AmigusLabs/BarcoSolar-2019/STL/sec6.stl

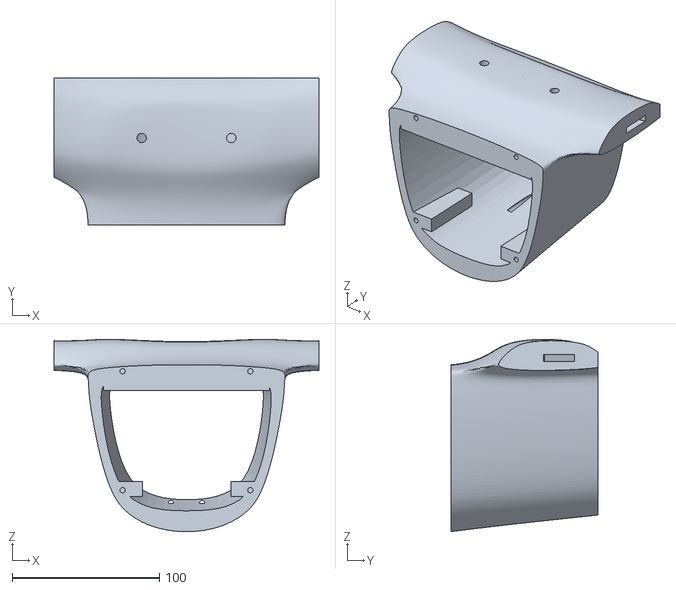
[picture p15: CAD file, 2019-10-26]
STL/sec6.stl
180.0 x 100.0 x 130.6
