AmigusLabs/BarcoSolar-2019/STL/soporte_servo.stl

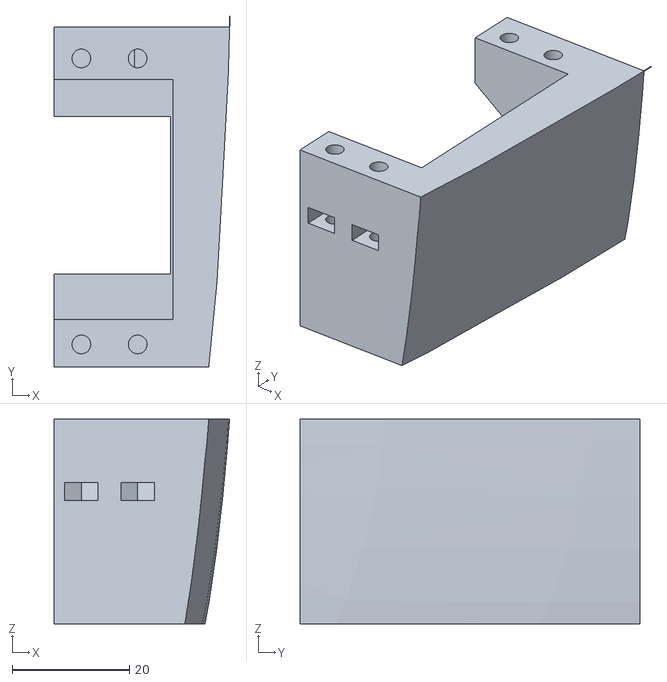
[picture p16: CAD file, 2019-10-26]
STL/soporte_servo.stl
30.0 x 59.9 x 35.0
