AmigusLabs/BarcoSolar-2019/STL/sec8.stl

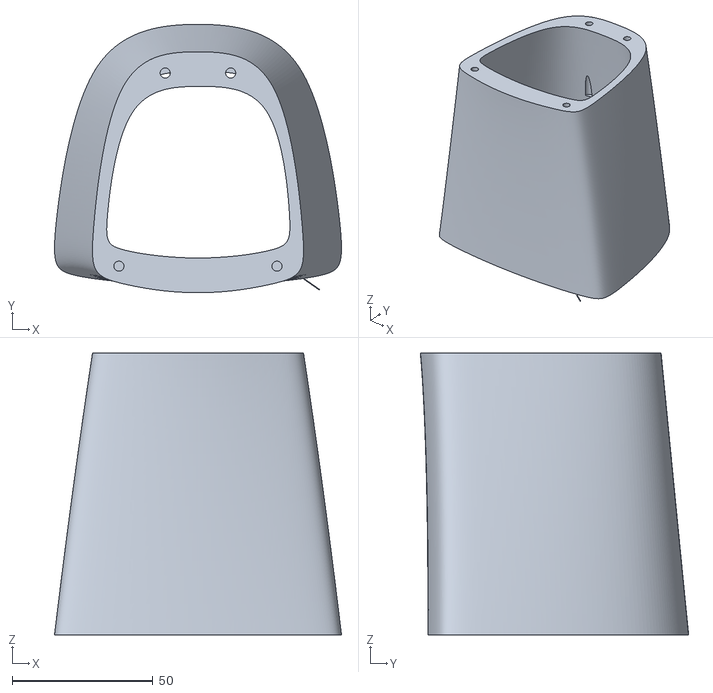
[picture p17: CAD file, 2019-10-26]
STL/sec8.stl
101.9 x 95.3 x 100.0
