AmigusLabs/BarcoSolar-2019/STL/soporte_arduino.stl

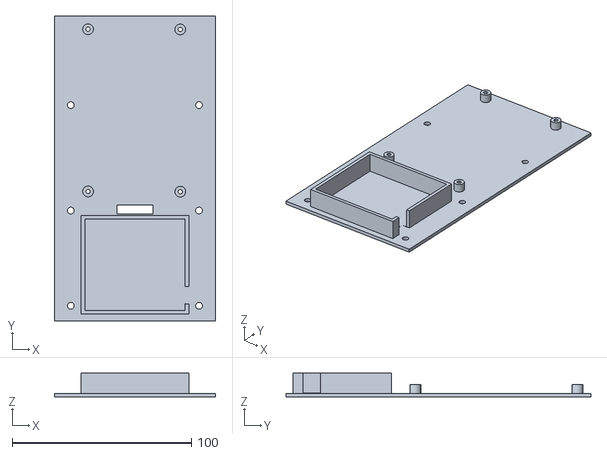
[picture p18: CAD file, 2019-10-26]
STL/soporte_arduino.stl
90.0 x 170.0 x 13.3
