AmigusLabs/BarcoSolar-2019/STL/tapa_barco.stl

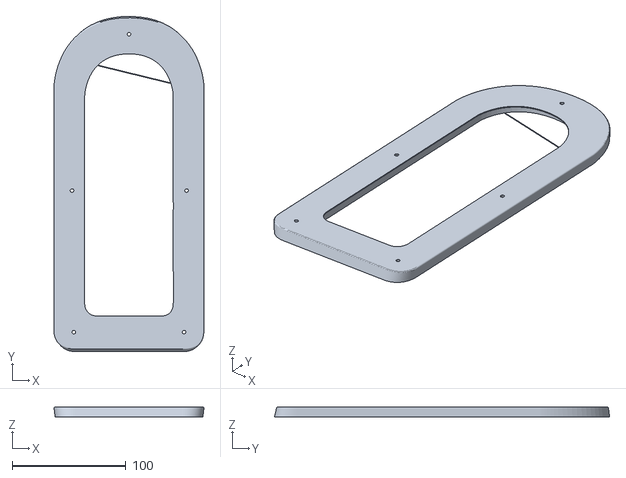
[picture p19: CAD file, 2019-10-26]
STL/tapa_barco.stl
132.0 x 295.0 x 9.02
