AmigusLabs/BarcoSolar-2019/STL/soporte_balsa_der.stl

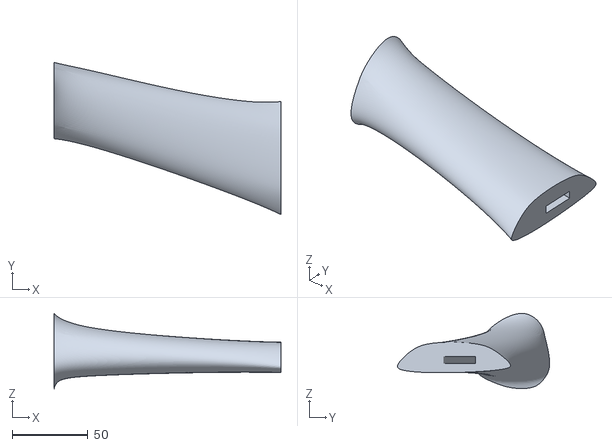
[picture p20: CAD file, 2019-10-26]
STL/soporte_balsa_der.stl
150.0 x 100.6 x 49.7
