AmigusLabs/BarcoSolar-2019/STL/sec1.stl

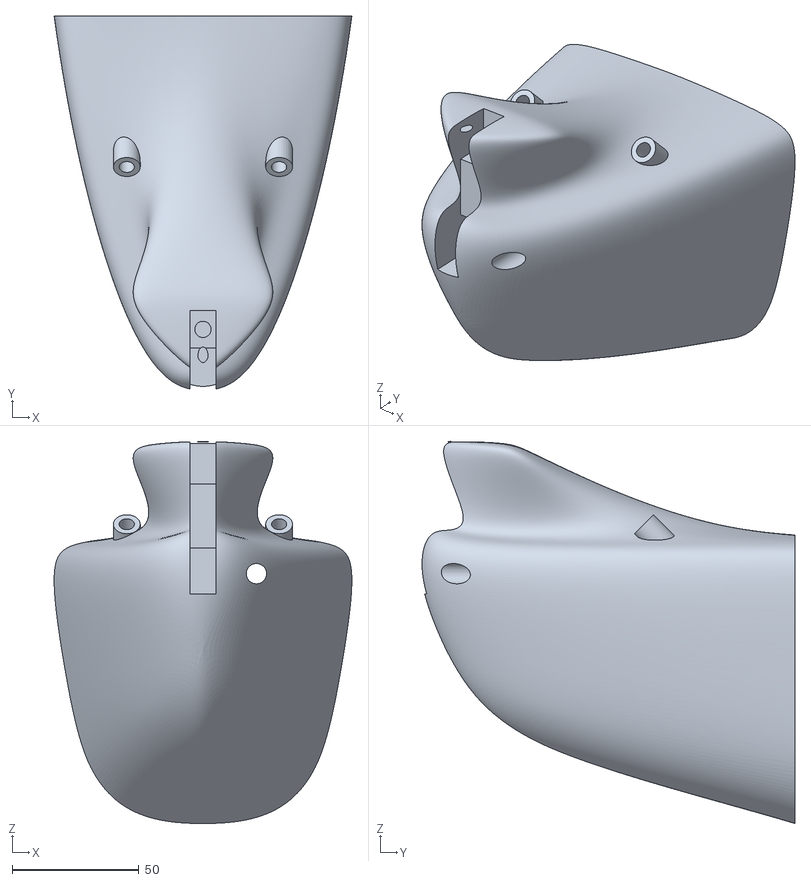
[picture p21: CAD file, 2019-10-26]
STL/sec1.stl
117.3 x 146.9 x 150.5
