AmigusLabs/BarcoSolar-2019/STL/timon2.stl

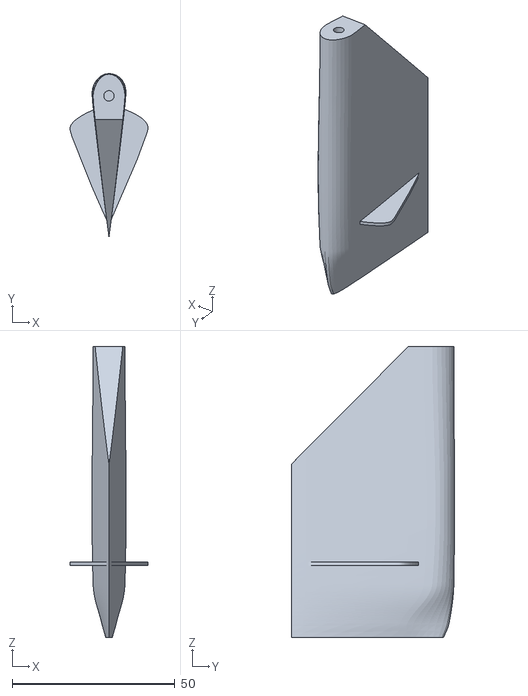
[picture p22: CAD file, 2019-10-26]
STL/timon2.stl
24.0 x 50.1 x 89.5
