AmigusLabs/BarcoSolar-2019/STL/eje_y_timon.stl

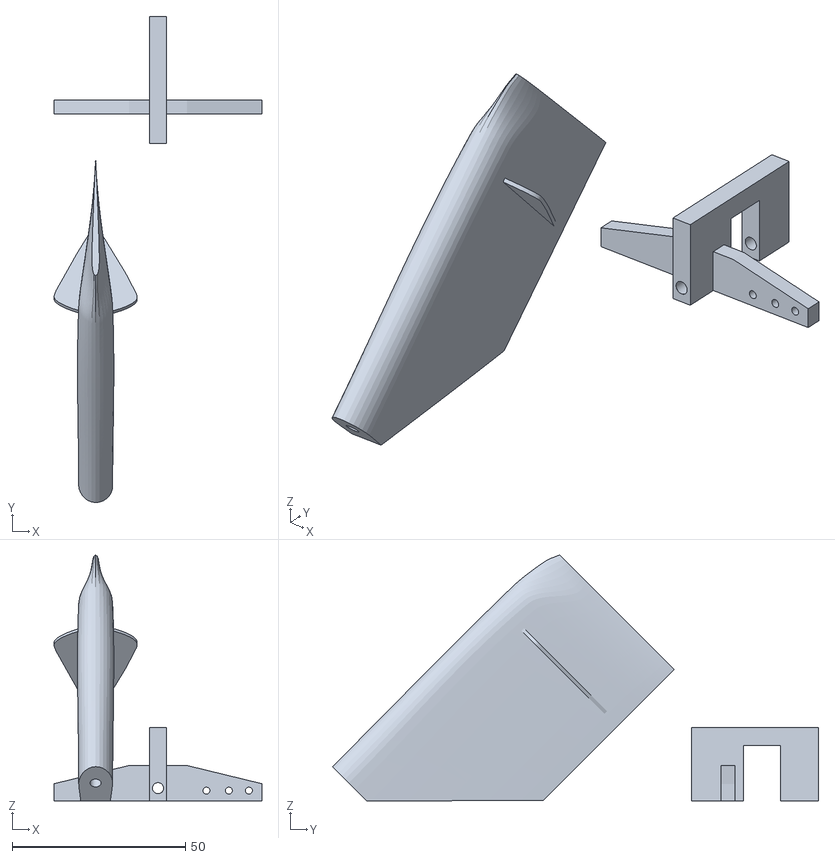
[picture p23: CAD file, 2019-10-26]
STL/eje_y_timon.stl
60.0 x 140.2 x 71.0
