AmigusLabs/BarcoSolar-2019/STL/soporte_motor_PLA.stl

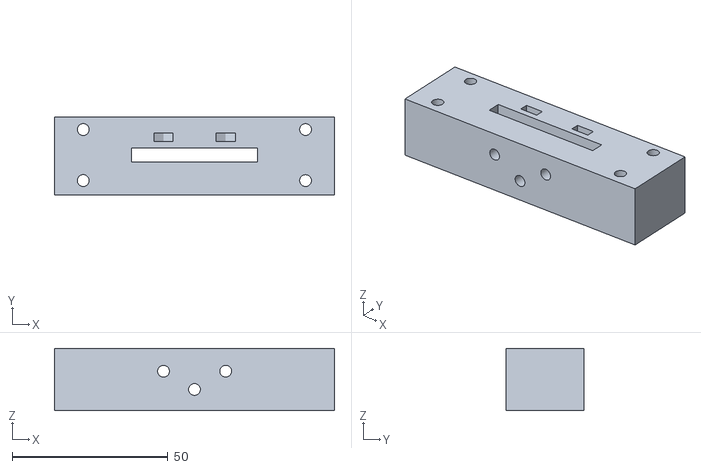
[picture p24: CAD file, 2019-10-26]
STL/soporte_motor_PLA.stl
90.0 x 25.0 x 20.0
