AmigusLabs/BarcoSolar-2019/STL/sec10.stl

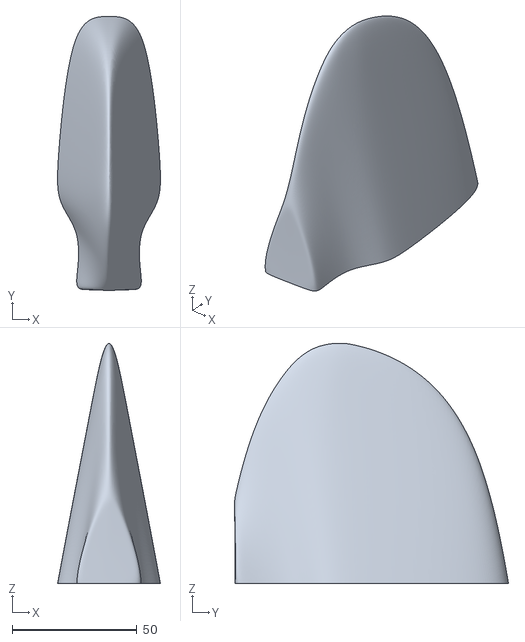
[picture p25: CAD file, 2019-10-26]
STL/sec10.stl
41.2 x 109.8 x 96.3
