AmigusLabs/BarcoSolar-2019/STL/sec5.stl

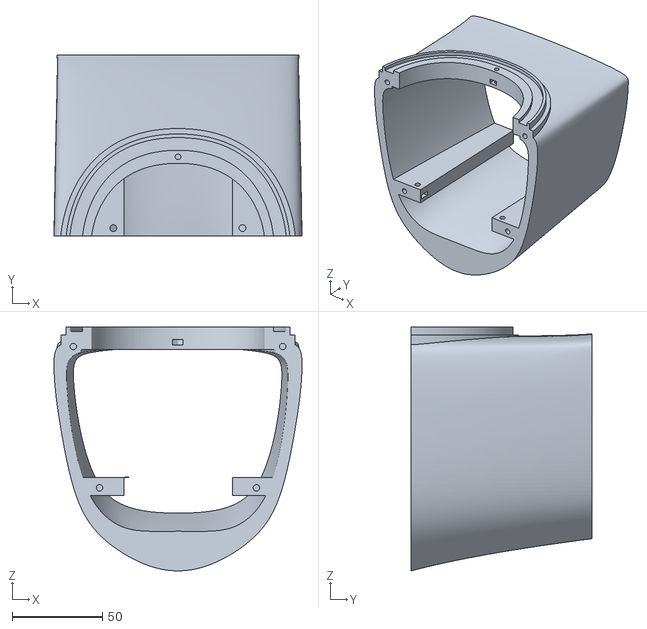
[picture p26: CAD file, 2019-10-26]
STL/sec5.stl
137.2 x 100.1 x 134.9
