AmigusLabs/BarcoSolar-2019/STL/soporte_balsa_izq.stl

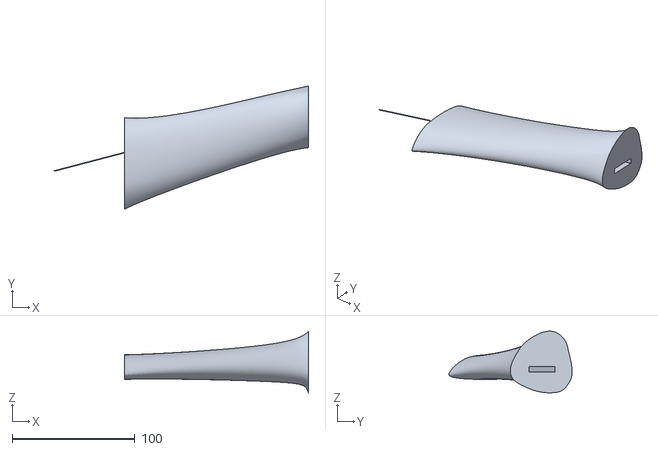
[picture p27: CAD file, 2019-10-26]
STL/soporte_balsa_izq.stl
207.2 x 100.5 x 50.3
