AmigusLabs/BarcoSolar-2019/STL/soporte_balsa_izq_3.stl

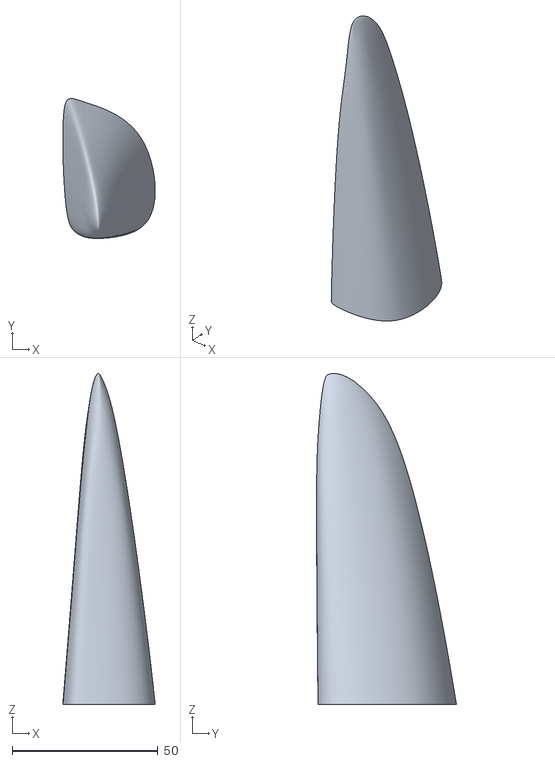
[picture p28: CAD file, 2019-10-26]
STL/soporte_balsa_izq_3.stl
31.8 x 48.1 x 113.7
