AmigusLabs/BarcoSolar-2019/STL/sec6_soporte.stl

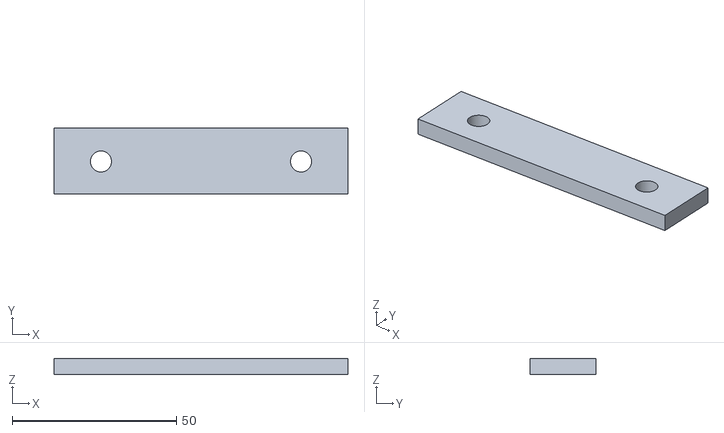
[picture p29: CAD file, 2019-10-26]
STL/sec6_soporte.stl
89.5 x 20.0 x 5.00
