AmigusLabs/BarcoSolar-2019/STL/sec4.stl

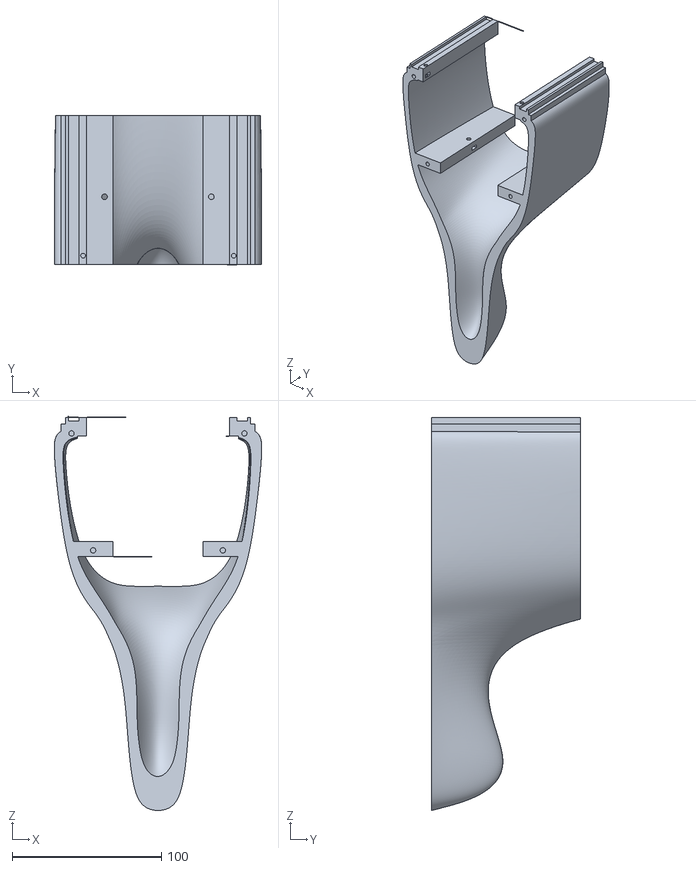
[picture p30: CAD file, 2019-10-26]
STL/sec4.stl
138.8 x 100.1 x 263.7
