AmigusLabs/BarcoSolar-2019/STL/eje_timon.stl

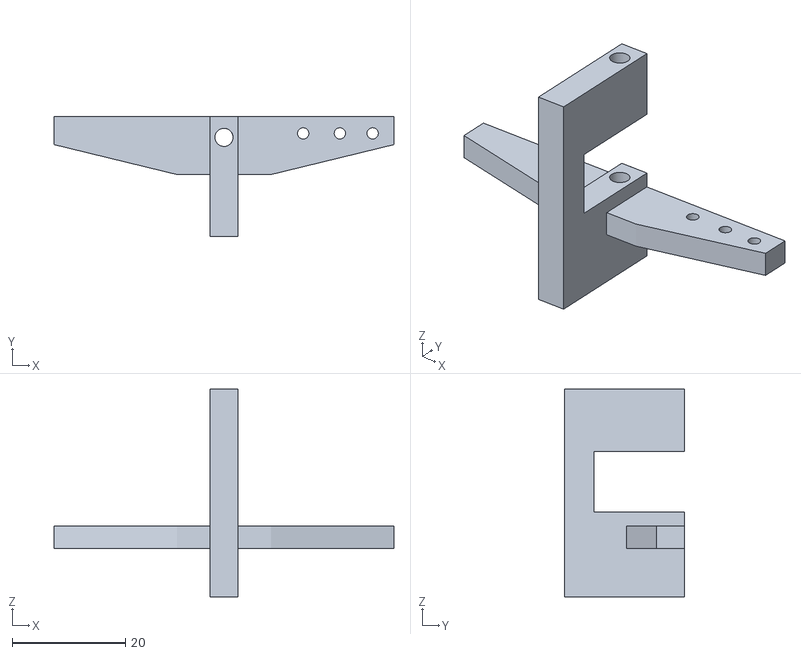
[picture p31: CAD file, 2019-10-26]
STL/eje_timon.stl
60.0 x 21.2 x 36.6
