AmigusLabs/BarcoSolar-2019/STL/sec7.stl

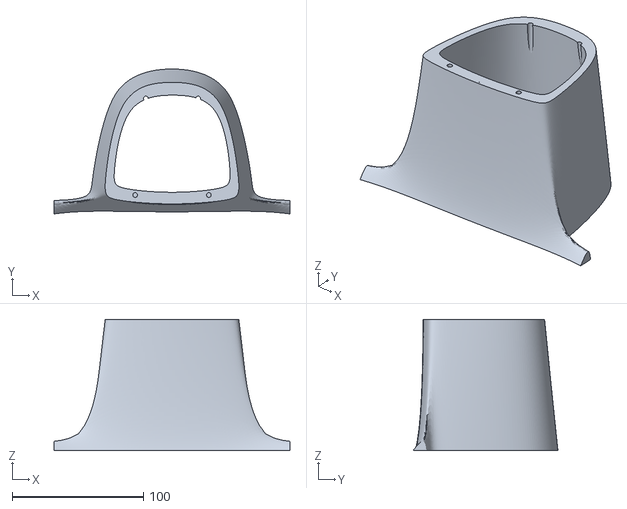
[picture p32: CAD file, 2019-10-26]
STL/sec7.stl
180.0 x 110.5 x 100.0
