AmigusLabs/BarcoSolar-2019/STL/sec9.stl

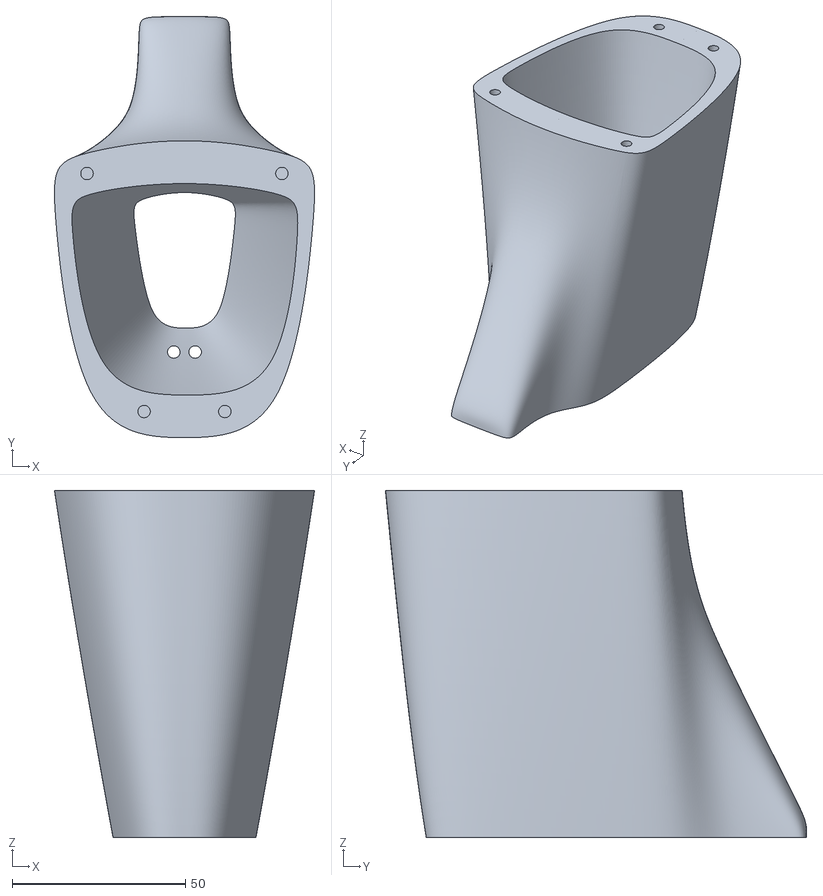
[picture p33: CAD file, 2019-10-26]
STL/sec9.stl
75.0 x 121.4 x 100.0
